ManuCorrea/Quadruped/quadrupedSTLs/Extras/ADNS_2.stl

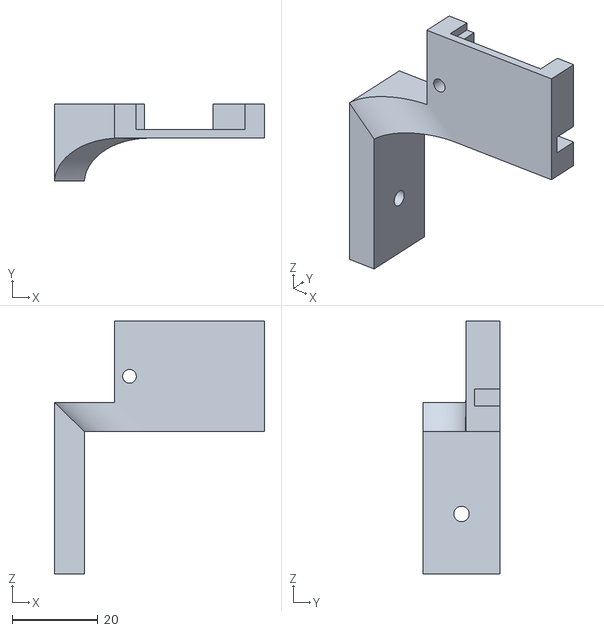
[picture p15: CAD file, 2020-02-17]
quadrupedSTLs/Extras/ADNS_2.stl
49.0 x 18.0 x 59.0
