ManuCorrea/Quadruped/quadrupedSTLs/femurGear.stl

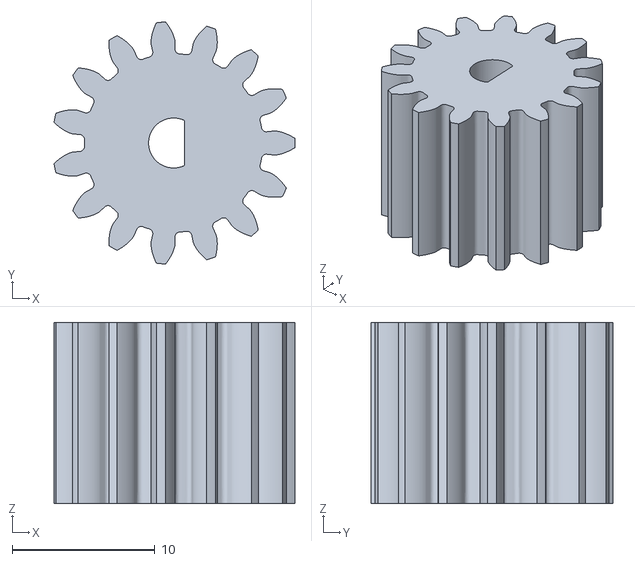
[picture p16: CAD file, 2020-02-17]
quadrupedSTLs/femurGear.stl
16.9 x 17.0 x 12.7
