ManuCorrea/Quadruped/URDF_Quadruped/STLs/Femur.stl

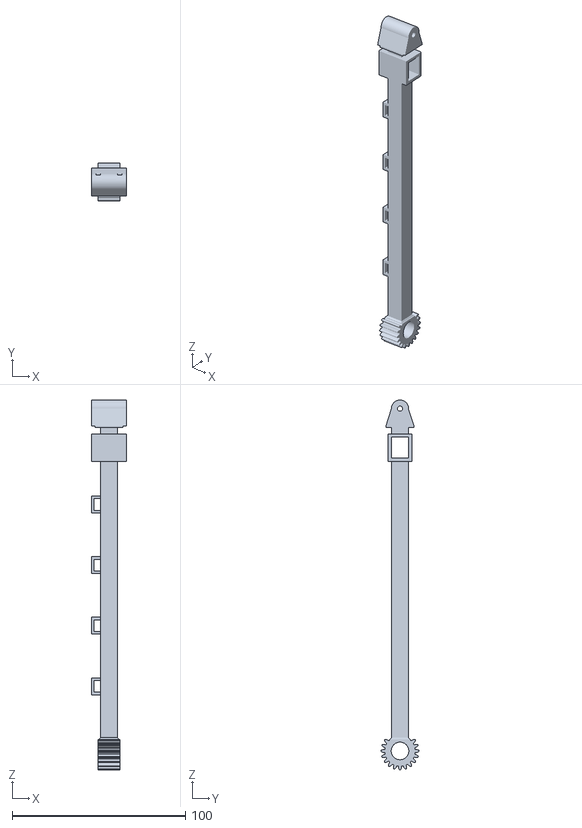
[picture p17: CAD file, 2020-02-17]
URDF_Quadruped/STLs/Femur.stl
20.0 x 22.0 x 213.7
