ManuCorrea/Quadruped/quadrupedSTLs/tibia.stl

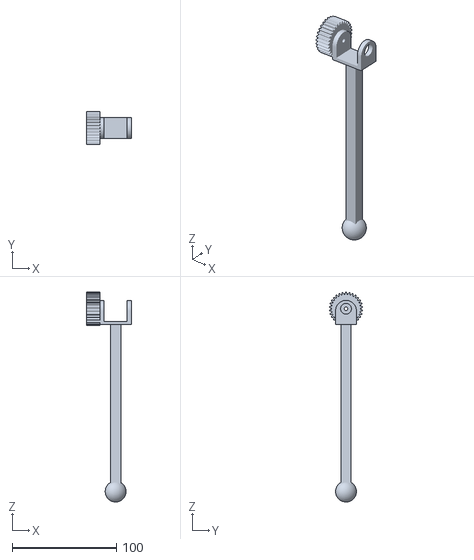
[picture p18: CAD file, 2020-02-17]
quadrupedSTLs/tibia.stl
42.7 x 31.9 x 201.0
