ManuCorrea/Quadruped/URDF_Quadruped/STLs/HombroSoporte.stl

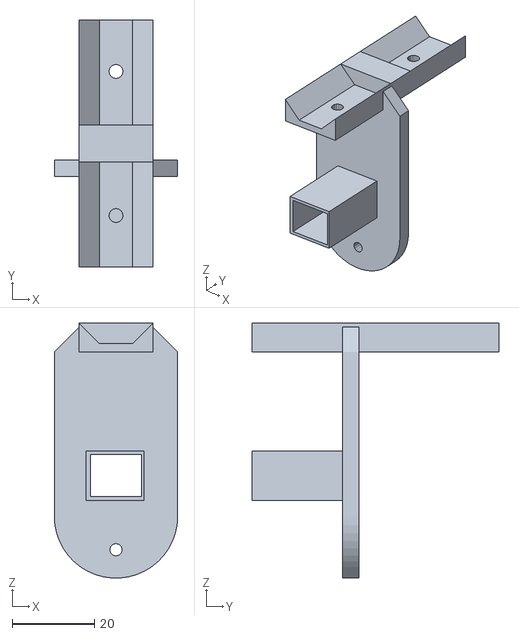
[picture p19: CAD file, 2020-02-17]
URDF_Quadruped/STLs/HombroSoporte.stl
30.0 x 60.0 x 62.0
