ManuCorrea/Quadruped/URDF_Quadruped/STLs/Tibia.stl

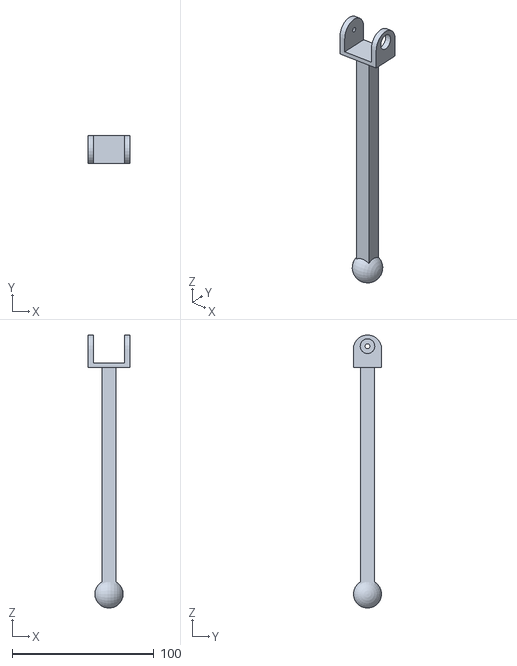
[picture p20: CAD file, 2020-02-17]
URDF_Quadruped/STLs/Tibia.stl
30.0 x 20.0 x 192.8
